DylanMissu/Workshop11-samd/Workshop11Core-samd/variants/logger_zero/variant.h

/*
  Copyright (c) 2014-2015 Arduino LLC.  All right reserved.

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
  You should have received a copy of the GNU Lesser General Public
  License along with this library; if not, write to the Free Software
  Foundation, Inc., 51 Franklin St, Fifth Floor, Boston, MA  02110-1301  USA
*/

#ifndef _VARIANT_SODAQ_EXPLORER_
#define _VARIANT_SODAQ_EXPLORER_

// The definitions here needs a SAMD core >=1.6.10
#define ARDUINO_SAMD_VARIANT_COMPLIANCE 10610

/*----------------------------------------------------------------------------
 *        Definitions
 *----------------------------------------------------------------------------*/

/** Frequency of the board main oscillator */
#define VARIANT_MAINOSC       (32768ul)

/** Master clock frequency */
#define VARIANT_MCK           (48000000ul)

/** Copied from bootloader. It will cause a "stay in bootloader" when doing 1200bps-touch */
#define BOOT_DOUBLE_TAP_ADDRESS         (0x20007FFCul)
#define BOOT_DOUBLE_TAP_DATA            (*((volatile uint32_t *) BOOT_DOUBLE_TAP_ADDRESS))
#define DOUBLE_TAP_MAGIC                0x07738135

/*----------------------------------------------------------------------------
 *        Headers
 *----------------------------------------------------------------------------*/

#include "WVariant.h"

#ifdef __cplusplus
#include "SERCOM.h"
#include "Uart.h"
#endif // __cplusplus

#ifdef __cplusplus
extern "C"
{
#endif // __cplusplus

/*----------------------------------------------------------------------------
 *        Pins
 *----------------------------------------------------------------------------*/

// Number of pins defined in PinDescription array
#define PINS_COUNT           (49u)
#define NUM_DIGITAL_PINS     (20u)
#define NUM_ANALOG_INPUTS    (9u)
#define NUM_ANALOG_OUTPUTS   (1u)

#define digitalPinToPort(P)        ( &(PORT->Group[g_APinDescription[P].ulPort]) )
#define digitalPinToBitMask(P)     ( 1 << g_APinDescription[P].ulPin )
//#define analogInPinToBit(P)        ( )
#define portOutputRegister(port)   ( &(port->OUT.reg) )
#define portInputRegister(port)    ( &(port->IN.reg) )
#define portModeRegister(port)     ( &(port->DIR.reg) )
#define digitalPinHasPWM(P)        ( g_APinDescription[P].ulPWMChannel != NOT_ON_PWM || g_APinDescription[P].ulTCChannel != NOT_ON_TIMER )

/*
 * digitalPinToTimer(..) is AVR-specific and is not defined for SAMD
 * architecture. If you need to check if a pin supports PWM you must
 * use digitalPinHasPWM(..).
 *
 * https://github.com/arduino/Arduino/issues/1833
 */
// #define digitalPinToTimer(P)

// LEDs
#define LED_BLUE            (12u)
#define PIN_LED             LED_BLUE
#define LED_BUILTIN         LED_BLUE

#define LED_PINK            (13u)

// RESET LINES
#define LORA_RESET          (45u)

/*
 * Analog pins
 */
#define PIN_A0               (30ul)
#define PIN_A1               (PIN_A0 + 1)
#define PIN_A2               (PIN_A0 + 2)
#define PIN_A3               (PIN_A0 + 3)
#define PIN_A4               (PIN_A0 + 4)
#define PIN_A5               (PIN_A0 + 5)
#define PIN_A6               (PIN_A0 + 6)
#define PIN_A7               (PIN_A0 + 7)

#define PIN_INPUT1           (24ul)
#define PIN_INPUT2           (25ul)
#define PIN_INPUT3           (26ul)
#define PIN_INPUT4           (27ul)
#define PIN_INPUT5           (28ul)
#define PIN_INPUT6           (29ul)

static const uint8_t A0  = PIN_A0 ;
static const uint8_t A1  = PIN_A1 ;
static const uint8_t A2  = PIN_A2 ;
static const uint8_t A3  = PIN_A3 ;
static const uint8_t A4  = PIN_A4 ;
static const uint8_t A5  = PIN_A5 ;
static const uint8_t A6  = PIN_A6 ;
static const uint8_t A7  = PIN_A7 ;


static const uint8_t INPUT1  = PIN_INPUT1 ;
static const uint8_t INPUT2  = PIN_INPUT2 ;
static const uint8_t INPUT3  = PIN_INPUT3 ;
static const uint8_t INPUT4  = PIN_INPUT4 ;
static const uint8_t INPUT5  = PIN_INPUT5 ;
static const uint8_t INPUT6  = PIN_INPUT6 ;

#define ADC_RESOLUTION      12


static const uint8_t DAC0 = 43u ; // or (35u) implications for cores/arduino/wiring_analog.c analogWrite()


/*
 * Serial interfaces
 */
// Serial
#define PIN_SERIAL_RX       (0ul)
#define PIN_SERIAL_TX       (1ul)
#define PAD_SERIAL_TX       (UART_TX_PAD_0)
#define PAD_SERIAL_RX       (SERCOM_RX_PAD_1)

// Serial1
#define PIN_SERIAL1_RX       (30ul)
#define PIN_SERIAL1_TX       (29ul)
#define PAD_SERIAL1_TX       (UART_TX_PAD_2)
#define PAD_SERIAL1_RX       (SERCOM_RX_PAD_1)

// Serial2
#define PIN_SERIAL2_RX       (40ul)
#define PIN_SERIAL2_TX       (41ul)
#define PAD_SERIAL2_TX       (UART_TX_PAD_2)
#define PAD_SERIAL2_RX       (SERCOM_RX_PAD_1)

/*
 * SPI Interfaces
 */


#define SPI_INTERFACES_COUNT 1

// SPI
#define PIN_SPI_MISO         (37u)
#define PIN_SPI_SS           (38u)
#define PIN_SPI_MOSI         (39u)
#define PIN_SPI_SCK          (40u)

static const uint8_t MISO = PIN_SPI_MISO;
static const uint8_t SS   = PIN_SPI_SS ;
static const uint8_t SS_DFLASH  = 44 ;
static const uint8_t MOSI = PIN_SPI_MOSI ;
static const uint8_t SCK  = PIN_SPI_SCK ;


/*
 * Wire Interfaces
 */
#define WIRE_INTERFACES_COUNT 2

#define PIN_WIRE_SDA         (33u)
#define PIN_WIRE_SCL         (34u)

#define PIN_WIRE1_SDA        (35u)
#define PIN_WIRE1_SCL        (36u)


/*
 * USB
 */
#define PIN_USB_DM          (42ul)
#define PIN_USB_DP          (43ul)

#ifdef __cplusplus
}
#endif

/*----------------------------------------------------------------------------
 *        Arduino objects - C++ only
 *----------------------------------------------------------------------------*/

#ifdef __cplusplus

/*  =========================
 *  ===== SERCOM DEFINITION
 *  =========================
*/
extern SERCOM sercom0;
extern SERCOM sercom1;
extern SERCOM sercom2;
extern SERCOM sercom3;
extern SERCOM sercom4;
extern SERCOM sercom5;

extern Uart Serial;
extern Uart Serial1;
extern Uart Serial2;

#endif

// These serial port names are intended to allow libraries and architecture-neutral
// sketches to automatically default to the correct port name for a particular type
// of use.  For example, a GPS module would normally connect to SERIAL_PORT_HARDWARE_OPEN,
// the first hardware serial port whose RX/TX pins are not dedicated to another use.
//
// SERIAL_PORT_MONITOR        Port which normally prints to the Arduino Serial Monitor
//
// SERIAL_PORT_USBVIRTUAL     Port which is USB virtual serial
//
// SERIAL_PORT_LINUXBRIDGE    Port which connects to a Linux system via Bridge library
//
// SERIAL_PORT_HARDWARE       Hardware serial port, physical RX & TX pins.
//
// SERIAL_PORT_HARDWARE_OPEN  Hardware serial ports which are open for use.  Their RX & TX
//                            pins are NOT connected to anything by default.
#define SERIAL_PORT_USBVIRTUAL      SerialUSB
#define SERIAL_PORT_MONITOR         SerialUSB

// Serial has no physical pins broken out, so it's not listed as HARDWARE port
#define SERIAL_PORT_HARDWARE        Serial
#define SERIAL_PORT_HARDWARE_OPEN   Serial

#define SERIAL_PORT_HARDWARE1       Serial1
#define SERIAL_PORT_HARDWARE_OPEN1  Serial1

#define SERIAL_PORT_HARDWARE2       Serial2
#define SERIAL_PORT_HARDWARE_OPEN2  Serial2

#define PERIPH_WIRE                 sercom1
#define WIRE_IT_HANDLER             SERCOM1_Handler

#define PERIPH_WIRE1                sercom2
#define WIRE1_IT_HANDLER            SERCOM2_Handler

#define PERIPH_SPI                  sercom3
#define PAD_SPI_TX                  SPI_PAD_2_SCK_3
#define PAD_SPI_RX                  SERCOM_RX_PAD_0


#endif /* _VARIANT_SODAQ_EXPLORER */
